dmcke5/NucDeck/Buttons - STEP/Shoulder Button - Left.STEP

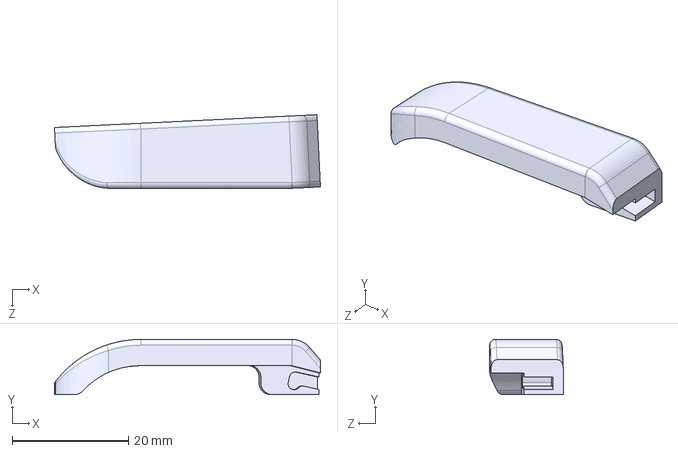
[picture p16: CAD file, 2023-08-07]
Buttons - STEP/Shoulder Button - Left.STEP
45.8 x 9.50 x 12.7 mm
