dmcke5/NucDeck/Housing - STEP/Left Side Grip.STEP

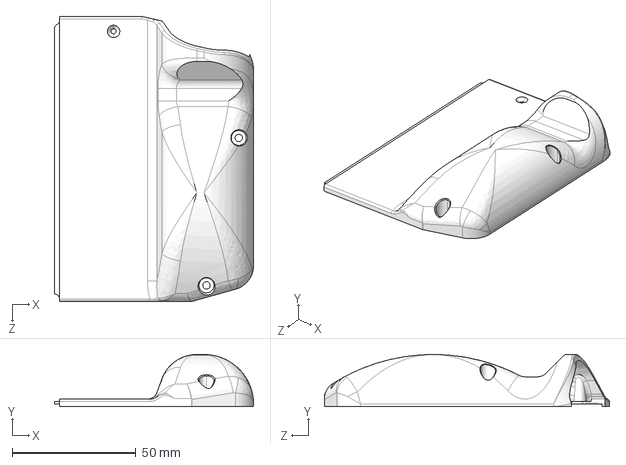
[picture p17: CAD file, 2023-08-07]
Housing - STEP/Left Side Grip.STEP
80.4 x 21.0 x 115.0 mm
