dmcke5/NucDeck/Buttons - STEP/Clicky Buttons - STEP/Action Button A - Clicky.STEP

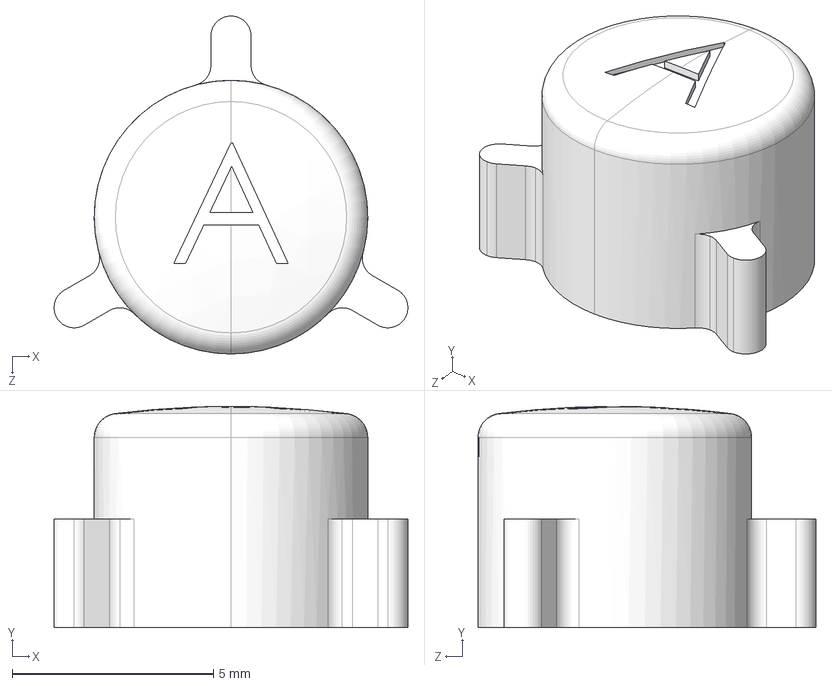
[picture p18: CAD file, 2023-08-07]
Buttons - STEP/Clicky Buttons - STEP/Action Button A - Clicky.STEP
8.79 x 5.50 x 8.40 mm
