dmcke5/NucDeck/Housing - STEP/Outlet Cover Plate 7th Gen Intel NUC.STEP

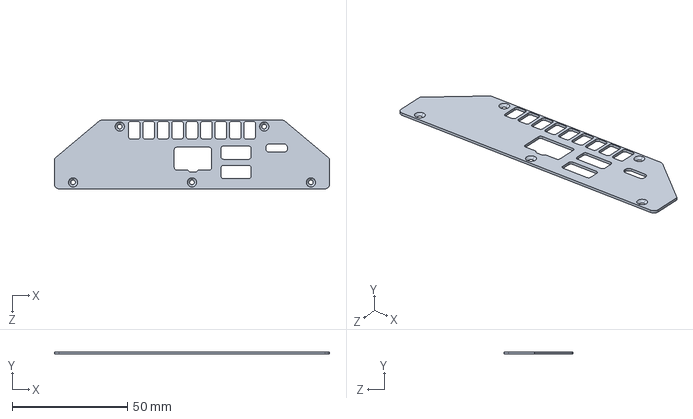
[picture p19: CAD file, 2023-08-07]
Housing - STEP/Outlet Cover Plate 7th Gen Intel NUC.STEP
119.1 x 1.00 x 29.8 mm
