dmcke5/NucDeck/Buttons - STEP/+ Volume Button.STEP

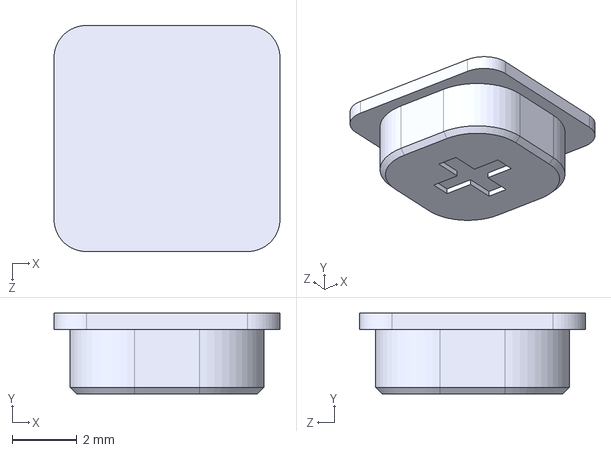
[picture p20: CAD file, 2023-08-07]
Buttons - STEP/+ Volume Button.STEP
7.00 x 2.50 x 7.00 mm
