dmcke5/NucDeck/Housing - STEP/Trigger Mount Left.STEP

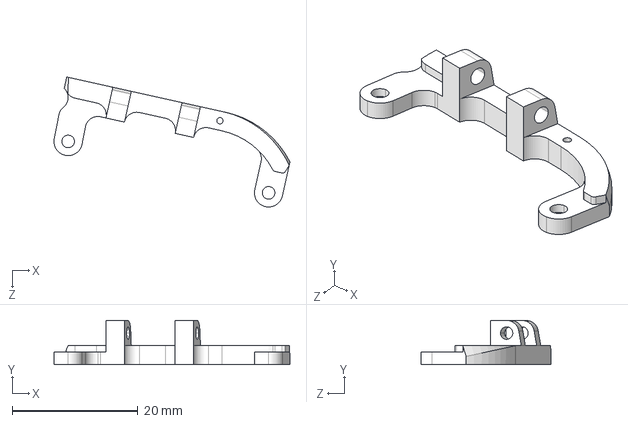
[picture p21: CAD file, 2023-08-07]
Housing - STEP/Trigger Mount Left.STEP
37.5 x 7.00 x 20.6 mm
