dmcke5/NucDeck/Buttons - STEP/Clicky Buttons - STEP/Action Button Y - Clicky.STEP

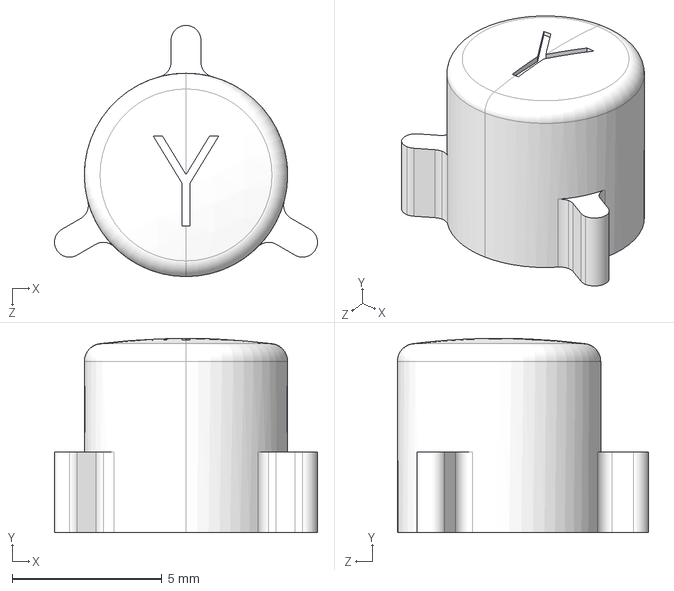
[picture p22: CAD file, 2023-08-07]
Buttons - STEP/Clicky Buttons - STEP/Action Button Y - Clicky.STEP
8.79 x 6.50 x 8.40 mm
