dmcke5/NucDeck/Buttons - STEP/Membrane Buttons - STEP/Action Button B - Standard.STEP

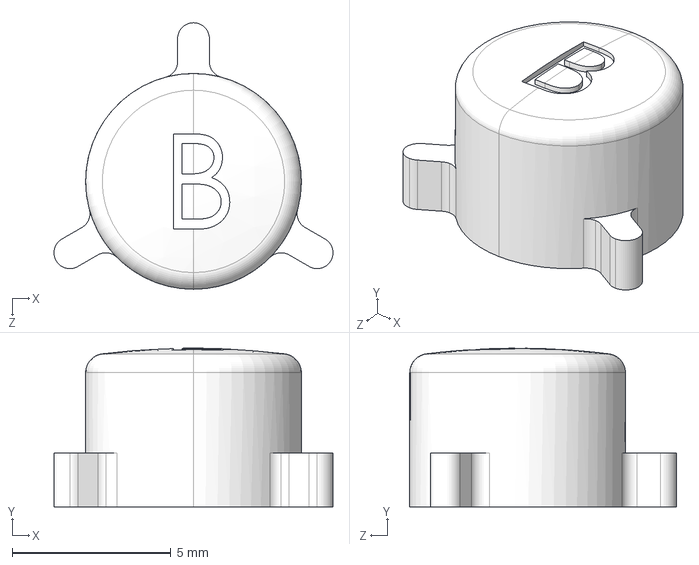
[picture p23: CAD file, 2023-08-07]
Buttons - STEP/Membrane Buttons - STEP/Action Button B - Standard.STEP
8.79 x 5.00 x 8.40 mm
