dmcke5/NucDeck/Buttons - STEP/Membrane Buttons - STEP/Action Button A - Standard.STEP

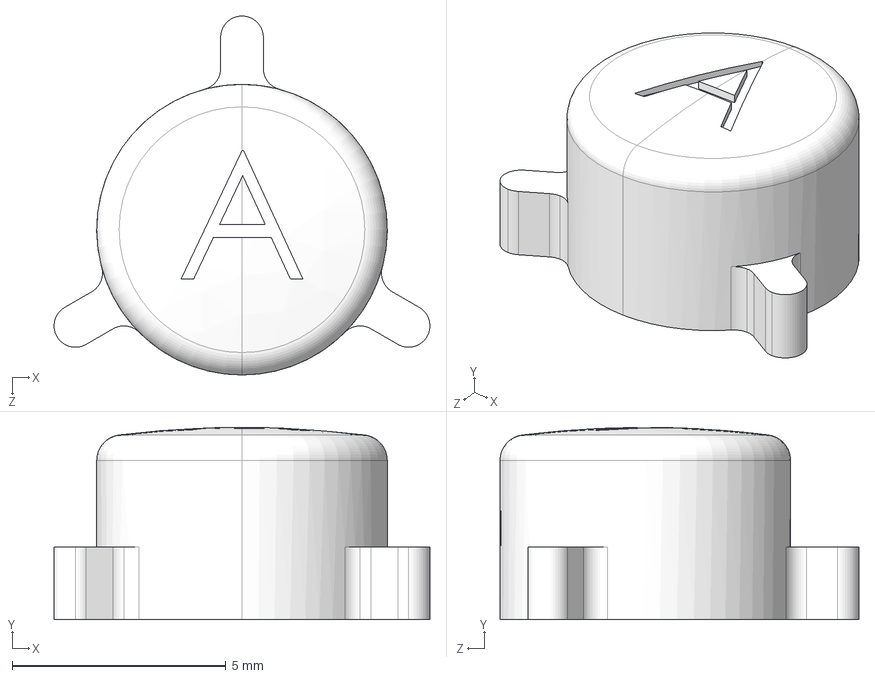
[picture p24: CAD file, 2023-08-07]
Buttons - STEP/Membrane Buttons - STEP/Action Button A - Standard.STEP
8.79 x 4.50 x 8.40 mm
