dmcke5/NucDeck/Buttons - STEP/Controller Mode Toggle.STEP

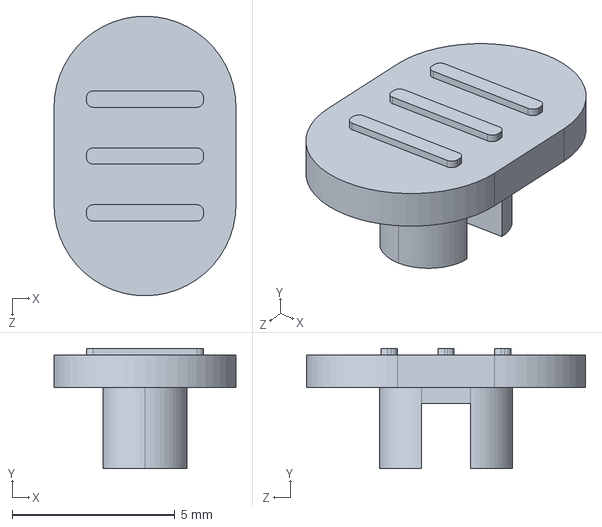
[picture p25: CAD file, 2023-08-07]
Buttons - STEP/Controller Mode Toggle.STEP
5.60 x 3.70 x 8.60 mm
