dmcke5/NucDeck/Housing - STEP/Joystick Surround Ring.STEP

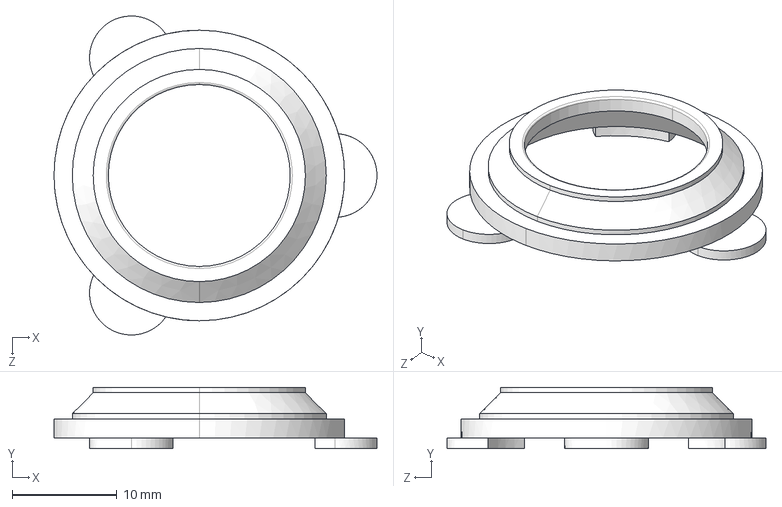
[picture p26: CAD file, 2023-07-30]
Housing - STEP/Joystick Surround Ring.STEP
30.9 x 5.85 x 30.5 mm
