dmcke5/NucDeck/Housing - STEP/Back Cover 7th Gen Intel NUC.STEP

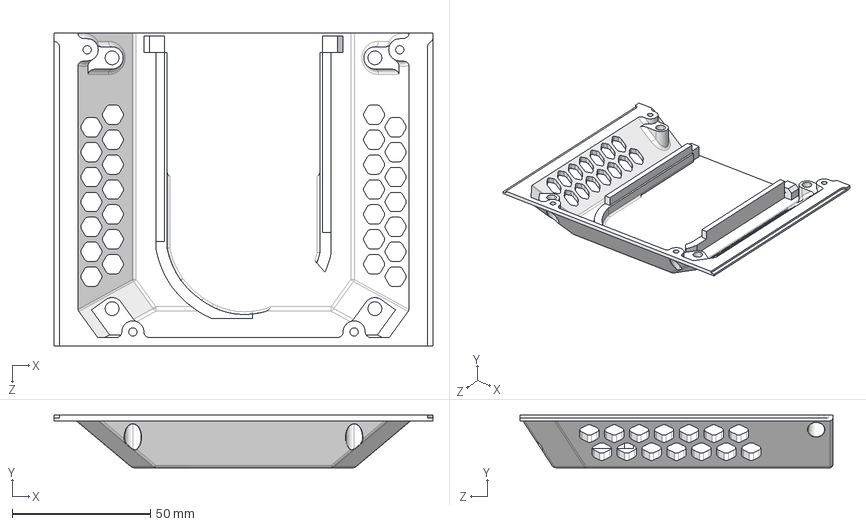
[picture p27: CAD file, 2023-07-30]
Housing - STEP/Back Cover 7th Gen Intel NUC.STEP
137.0 x 19.0 x 113.0 mm
