dmcke5/NucDeck/Software/Right Controller/NucDeck_Controller/images.h

//Images used in interface.
//Images are all monochrome bitmaps converted to XBM format using: https://www.online-utility.org/image/convert/to/XBM

#define keyboardWidth 43
#define keyboardHeight 25
#define gamepadWidth 43
#define gamepadHeight 25
#define splashWidth 80
#define splashHeight 160

//Icon for keyboard mode
PROGMEM const unsigned char keyboardIMG[] = {
  0xFE, 0xFF, 0xFF, 0xFF, 0xFF, 0x03, 0x03, 0x00, 0x00, 0x00, 0x00, 0x06, 
  0x01, 0x00, 0x00, 0x00, 0x00, 0x04, 0x71, 0x70, 0x70, 0x70, 0x70, 0x04, 
  0x89, 0x88, 0x88, 0x88, 0x88, 0x04, 0x89, 0x88, 0x88, 0x88, 0x88, 0x04, 
  0x89, 0x88, 0x88, 0x88, 0x88, 0x04, 0x71, 0x70, 0x70, 0x70, 0x70, 0x04, 
  0x01, 0x00, 0x00, 0x00, 0x00, 0x04, 0x01, 0x00, 0x00, 0x00, 0x00, 0x04, 
  0x71, 0x70, 0x70, 0x70, 0x70, 0x04, 0x89, 0x88, 0x88, 0x88, 0x88, 0x04, 
  0x89, 0x88, 0x88, 0x88, 0x88, 0x04, 0x89, 0x88, 0x88, 0x88, 0x88, 0x04, 
  0x71, 0x70, 0x70, 0x70, 0x70, 0x04, 0x01, 0x00, 0x00, 0x00, 0x00, 0x04, 
  0x01, 0x00, 0x00, 0x00, 0x00, 0x04, 0x71, 0xF0, 0xFF, 0x7F, 0x70, 0x04, 
  0x89, 0x08, 0x00, 0x80, 0x88, 0x04, 0x89, 0x08, 0xF8, 0x81, 0x88, 0x04, 
  0x89, 0x08, 0x00, 0x80, 0x88, 0x04, 0x71, 0xF0, 0xFF, 0x7F, 0x70, 0x04, 
  0x01, 0x00, 0x00, 0x00, 0x00, 0x04, 0x03, 0x00, 0x00, 0x00, 0x00, 0x06, 
  0xFE, 0xFF, 0xFF, 0xFF, 0xFF, 0x03, };

//Icon for gamepad mode
PROGMEM const unsigned char gamepadIMG[] = {
  0xFC, 0xFD, 0xFF, 0xFF, 0xFD, 0x01, 0xFE, 0x03, 0x00, 0x00, 0xFE, 0x03, 
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
  0x01, 0x00, 0x60, 0xC0, 0x01, 0x00, 0x30, 0x80, 0xF1, 0x80, 0x01, 0x00, 
  0x60, 0x80, 0x03, 0x00, 0x30, 0x80, 0xB1, 0x81, 0x01, 0x00, 0x60, 0x00, 
  0x03, 0x00, 0x30, 0x80, 0x31, 0x83, 0x0D, 0x86, 0x67, 0x00, 0xE6, 0x83, 
  0x37, 0x9C, 0x31, 0x86, 0x0D, 0xE6, 0x6F, 0x00, 0xF6, 0xE7, 0x3F, 0x8E, 
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
