dmcke5/NucDeck/Software/Right Controller/NucDeck_Controller/max17261.ino

//Max17261 register addresses
byte max17261Addr = 0x36;
static int Status = 0x00;
static int VCell = 0x09;
//static int AvgVCell = 0x19; Unused
static int Current = 0x0A;
static int AvgCurrent = 0x0B;
static int RepSOC = 0x06;
static int RepCap = 0x05;
static int TimeToEmpty = 0x11;
static int DesignCap = 0x18;

//Battery Configuration
int batteryCapacity = 3000;       //Original Battery Capacity in mAh
float ChargeVoltage = 4.2;        //Maximum charge voltage per cell. Used for SOC calculations, this will NOT change the actual charge voltage of the battery.
int max17261_Status = 0;          //Fuel Gauge Status stored here
float lowVoltageThreshold = 3.1;  //Empty voltage threshold. Used for SOC calculation only

//Multiplication factors for fuel gauge info
static float capacity_multiplier_mAH = (5e-3)/0.01;
static float current_multiplier_mV = 0.00015625;
static float voltage_multiplier_V = 7.8125e-5;
static float time_multiplier_Hours = 5.625/3600.0;
static float percentage_multiplier = 1.0/256.0;

void WriteRegister(int addr, int reg, int value){ //Write Fuel gauge i2c register
  Wire.beginTransmission(addr);
  Wire.write(reg);
  byte byte1 = value >> 8;
  byte byte2 = value & 0xFF;
  Wire.write(byte2);
  Wire.write(byte1);
  Wire.endTransmission();
}

int ReadRegister(int addr, int reg){ //Read fuel gauge i2c register
  Wire.beginTransmission(addr);
  Wire.write(reg);
  Wire.endTransmission();
  Wire.requestFrom(addr,2,true);
  while (Wire.available()) {
    int readingLow = Wire.read();
    int readingHigh = Wire.read();
    return(word(readingHigh, readingLow));
  }
  return 0;
}

#define MAX17261_VEMPTY_REG(ve_mv, vr_mv)\      //Define vempty reg
  ((((ve_mv * 1000) / 10) << 7) | (vr_mv / 40))

float getSOC() { //Returns state of charge as a percentage.
  int SOC_raw = ReadRegister(max17261Addr, RepSOC);
  return SOC_raw * percentage_multiplier;
}

int getCapacity() { //Returns configured battery capacity in mAh
  int capacity_raw = ReadRegister(max17261Addr, DesignCap);
  capacity_raw = capacity_raw * capacity_multiplier_mAH;
  return (capacity_raw);
}

int getRemainingCapacity() { //Returns remaining capacity in mAh
  int remainingCapacity_raw = ReadRegister(max17261Addr, RepCap);
  remainingCapacity_raw = remainingCapacity_raw * capacity_multiplier_mAH;
  return (remainingCapacity_raw);
}

float getInstantaneousCurrent() { //Returns current in Amps
  int16_t current_raw = ReadRegister(max17261Addr, Current);
  return current_raw * current_multiplier_mV;
}

float getAverageCurrent() { //Returns Average current in Amps
  int16_t current_raw = ReadRegister(max17261Addr, AvgCurrent);
  return current_raw * current_multiplier_mV;
}

float getInstantaneousVoltage() { //Returns voltage in volts
  int voltage_raw = ReadRegister(max17261Addr, VCell);
  return voltage_raw * voltage_multiplier_V;
}

float getTimeToEmpty() { //Returns time till empty as a decimal. Example 1.75 = 1 hour and 45 minutes
  int TTE_raw = ReadRegister(max17261Addr, TimeToEmpty);
  return TTE_raw * time_multiplier_Hours;
}

uint16_t getVEmpty() { //Returns configured empty voltage
  uint16_t VEmpty_raw = ReadRegister(max17261Addr, 0x3A);
  return (((VEmpty_raw >> 7) & 0x1FF) * 10);
}

void max17261Init(){ //Fuel gauge initialisation
  int StatusPOR = ReadRegister(max17261Addr,0x00) & 0x0002;
  int currentCapacity;

  if(StatusPOR == 0){
    Serial.println("POR = 0");
    getCapacity();
    getSOC();
  } else {
    Serial.println("test1");
    Serial.println(ReadRegister(max17261Addr, 0x3D) & 1);
    while (ReadRegister(max17261Addr, 0x3D) & 1) {
      delay(10);
    }
    Serial.println("test2");
    WriteRegister(max17261Addr, 0x18, (batteryCapacity / capacity_multiplier_mAH)); //Write DesignCap
    WriteRegister(max17261Addr, 0x45, (int)(batteryCapacity / capacity_multiplier_mAH) / 32); //Write dQAcc
    WriteRegister(max17261Addr, 0x1E, 0x666); //256mA); //Write IchgTerm
    WriteRegister(max17261Addr, 0x3A, MAX17261_VEMPTY_REG((int)lowVoltageThreshold, 3880)); //3.1V //Write VEmpty
    int HibCFG = ReadRegister(max17261Addr, 0xBA); //Store original HibCFG value
    WriteRegister(max17261Addr, 0x60, 0x90); //Exit Hibernate Mode Step 1
    WriteRegister(max17261Addr, 0xBA, 0x0); //Exit Hibernate Mode Step 2
    WriteRegister(max17261Addr, 0x60, 0x0); //Exit Hibernate Mode Step 3

    if (ChargeVoltage > 4.275) {
      WriteRegister(max17261Addr, 0x46, (int)((batteryCapacity / capacity_multiplier_mAH) / 32) * 51200 / (batteryCapacity / capacity_multiplier_mAH));
      WriteRegister(max17261Addr, 0xDB, 0x8400);
    } else {
      WriteRegister(max17261Addr, 0x46, (int)((batteryCapacity / capacity_multiplier_mAH) / 32) * 44138 / (batteryCapacity / capacity_multiplier_mAH));
      WriteRegister(max17261Addr, 0xDB, 0x8000);
    }

    while (ReadRegister(max17261Addr, 0xDB) & 0x8000) {
      delay(10);
    }
    WriteRegister(max17261Addr, 0xBA, HibCFG);

    max17261_Status = ReadRegister(max17261Addr, 0x00);
    WriteRegister(max17261Addr, 0x00, Status & 0xFFFD);
  }
}
